Andrey-Prikupets/ForestLamp/docs/light_core_connections.jpg

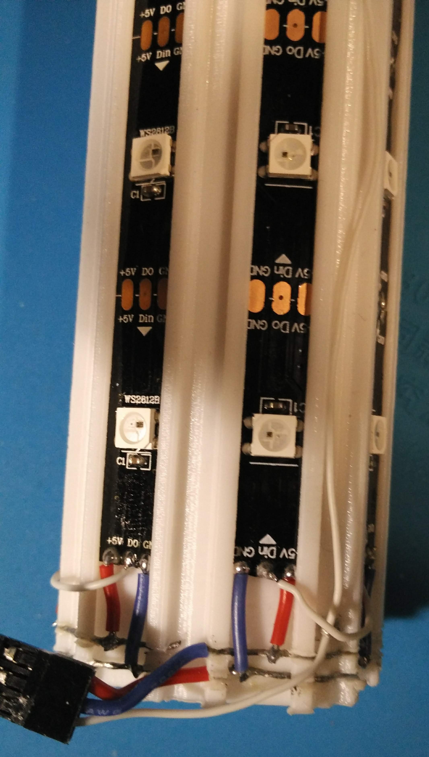
docs/light_core_connections.jpg
