Andrey-Prikupets/ForestLamp/docs/light_core_side_view.jpg

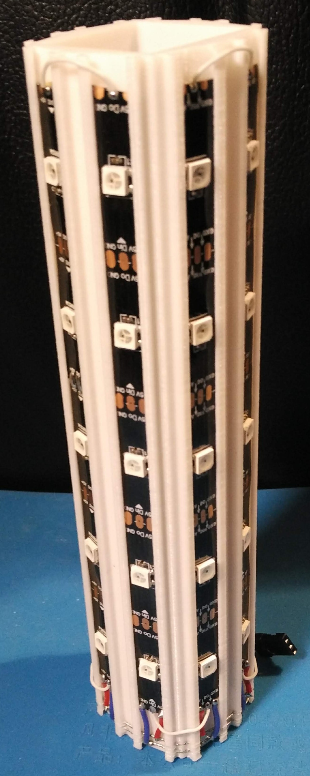
docs/light_core_side_view.jpg
