Andrey-Prikupets/ForestLamp/docs/light_core_top_view.jpg

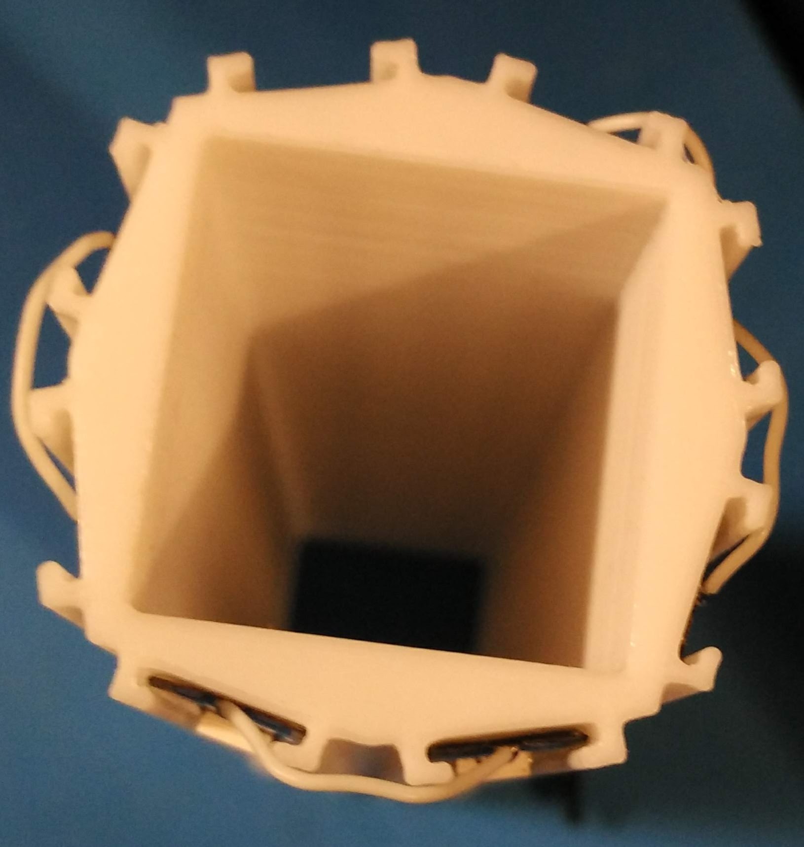
docs/light_core_top_view.jpg
