Andrey-Prikupets/ForestLamp/docs/light_core_with_cap1.jpg

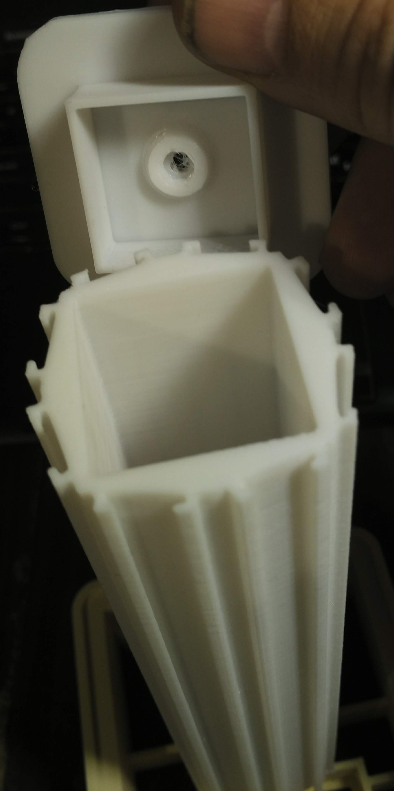
docs/light_core_with_cap1.jpg
