Andrey-Prikupets/ForestLamp/docs/light_cover_with_bottom_cap.jpg

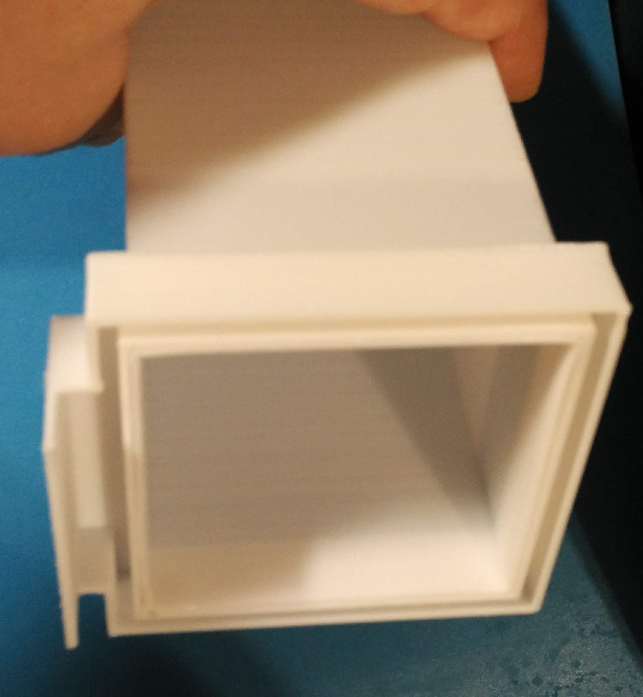
docs/light_cover_with_bottom_cap.jpg
