Andrey-Prikupets/ForestLamp/docs/light_cover_with_bottom_cap_side_view.jpg

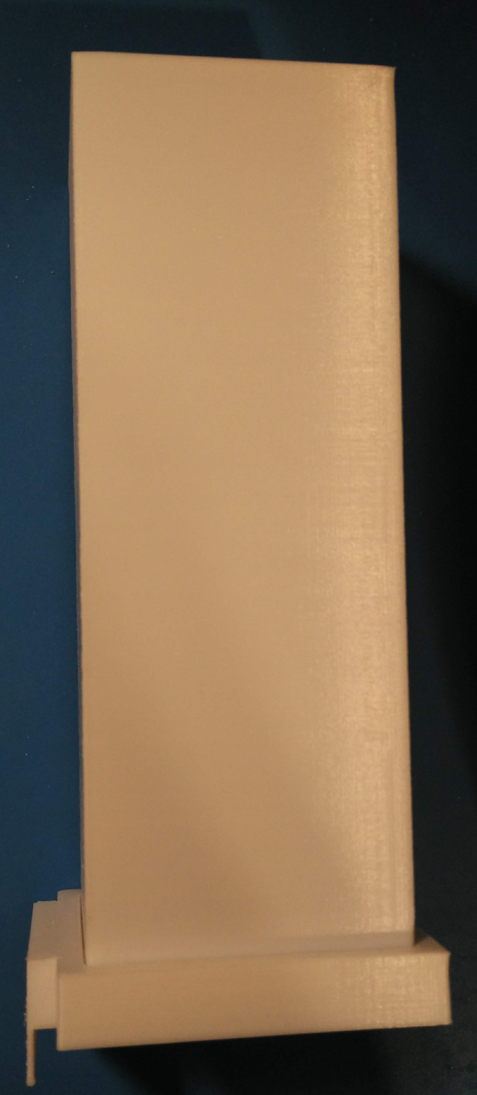
docs/light_cover_with_bottom_cap_side_view.jpg
