Andrey-Prikupets/ForestLamp/docs/top_cap_bottom_view.jpg

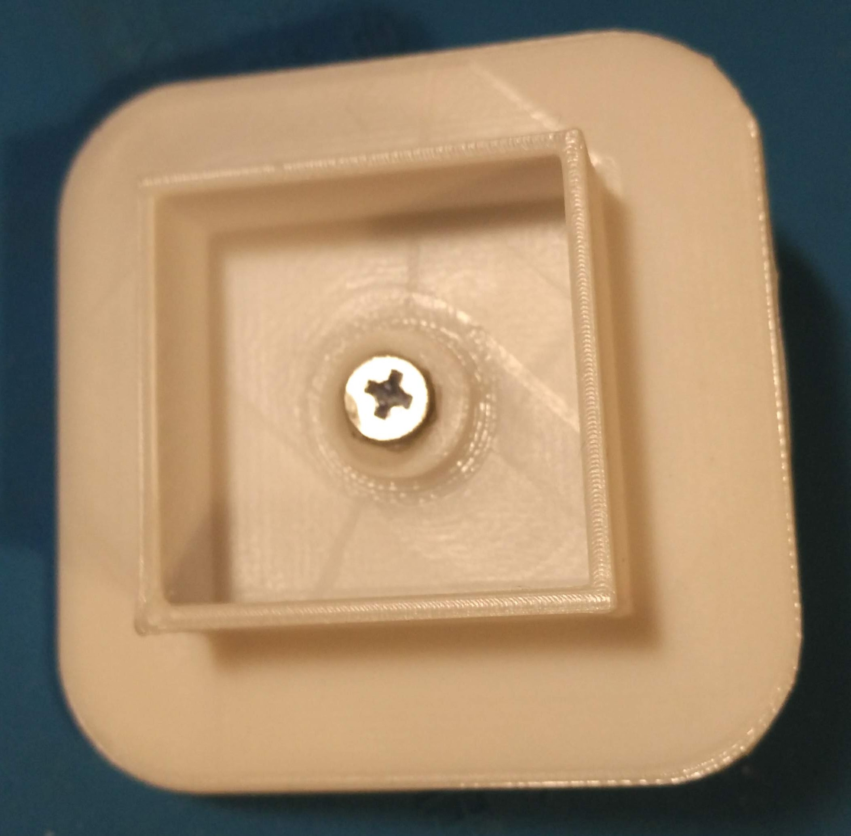
docs/top_cap_bottom_view.jpg
