Andrey-Prikupets/ForestLamp/docs/walls_assembled_bottom_view.jpg

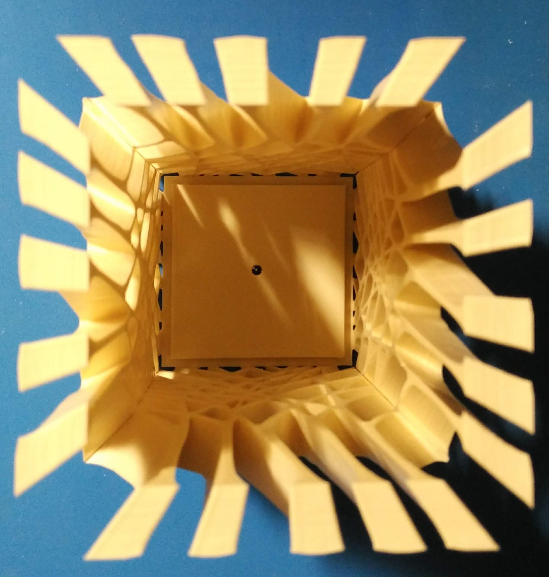
docs/walls_assembled_bottom_view.jpg
