Andrey-Prikupets/ForestLamp/docs/walls_assembled_top_view.jpg

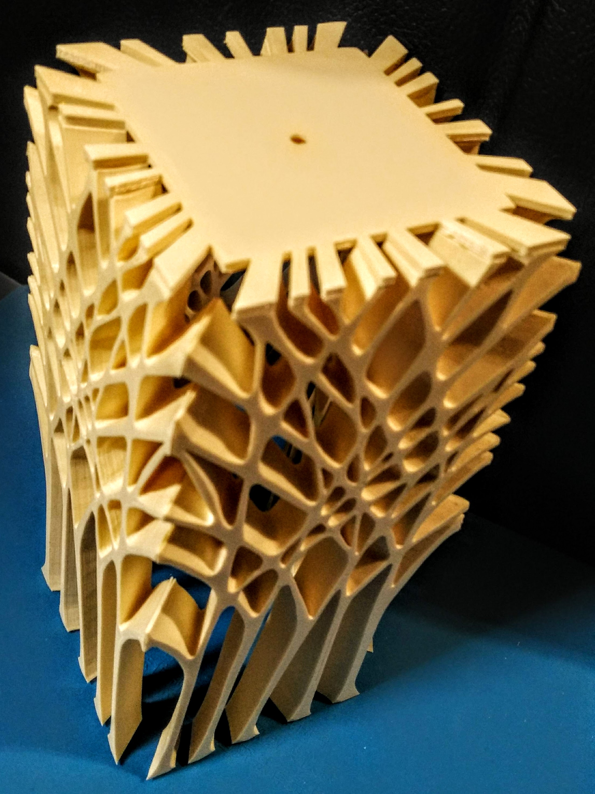
docs/walls_assembled_top_view.jpg
